blokidde/Blokboy-gaming-device/docs/assets/all_iterations.jpg

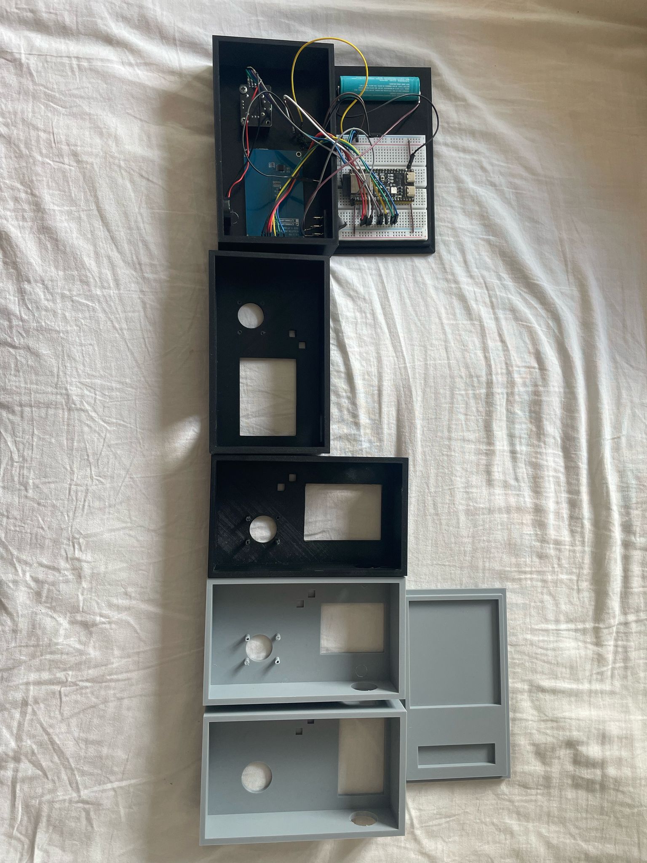
docs/assets/all_iterations.jpg
