blokidde/Blokboy-gaming-device/docs/assets/ardrone.jpeg

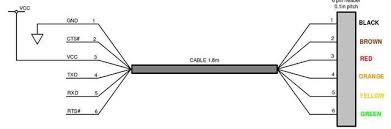
docs/assets/ardrone.jpeg
