blokidde/Blokboy-gaming-device/docs/assets/backpanel_v2.png

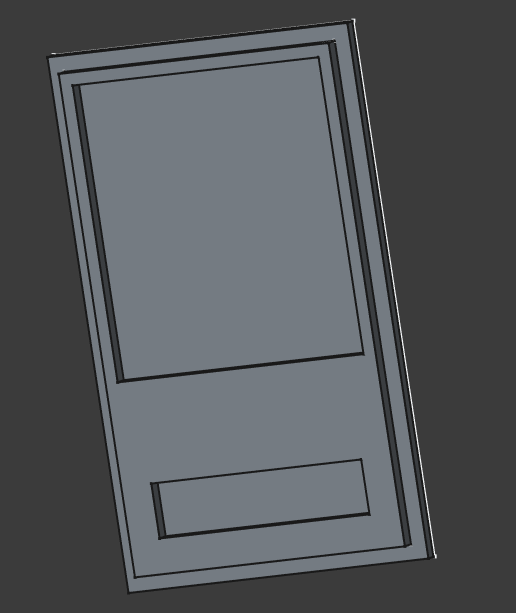
docs/assets/backpanel_v2.png
