blokidde/Blokboy-gaming-device/docs/assets/erd.png

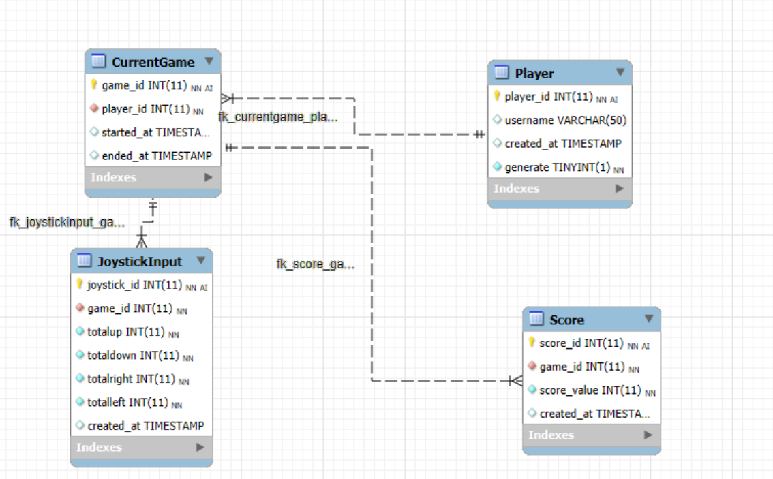
docs/assets/erd.png
