blokidde/Blokboy-gaming-device/docs/assets/frontpanel_v5.png

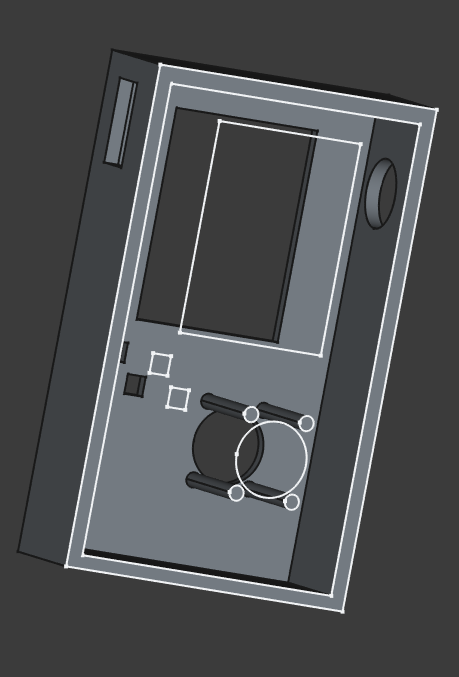
docs/assets/frontpanel_v5.png
