blokidde/Blokboy-gaming-device/docs/assets/http_json_mess.png

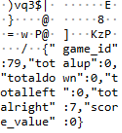
docs/assets/http_json_mess.png
