blokidde/Blokboy-gaming-device/docs/assets/http_message_info.png

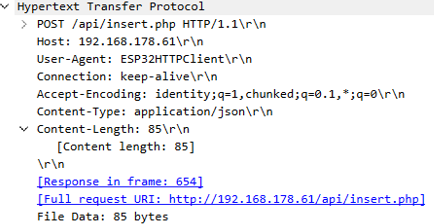
docs/assets/http_message_info.png
