blokidde/Blokboy-gaming-device/docs/assets/http_wireshark.png

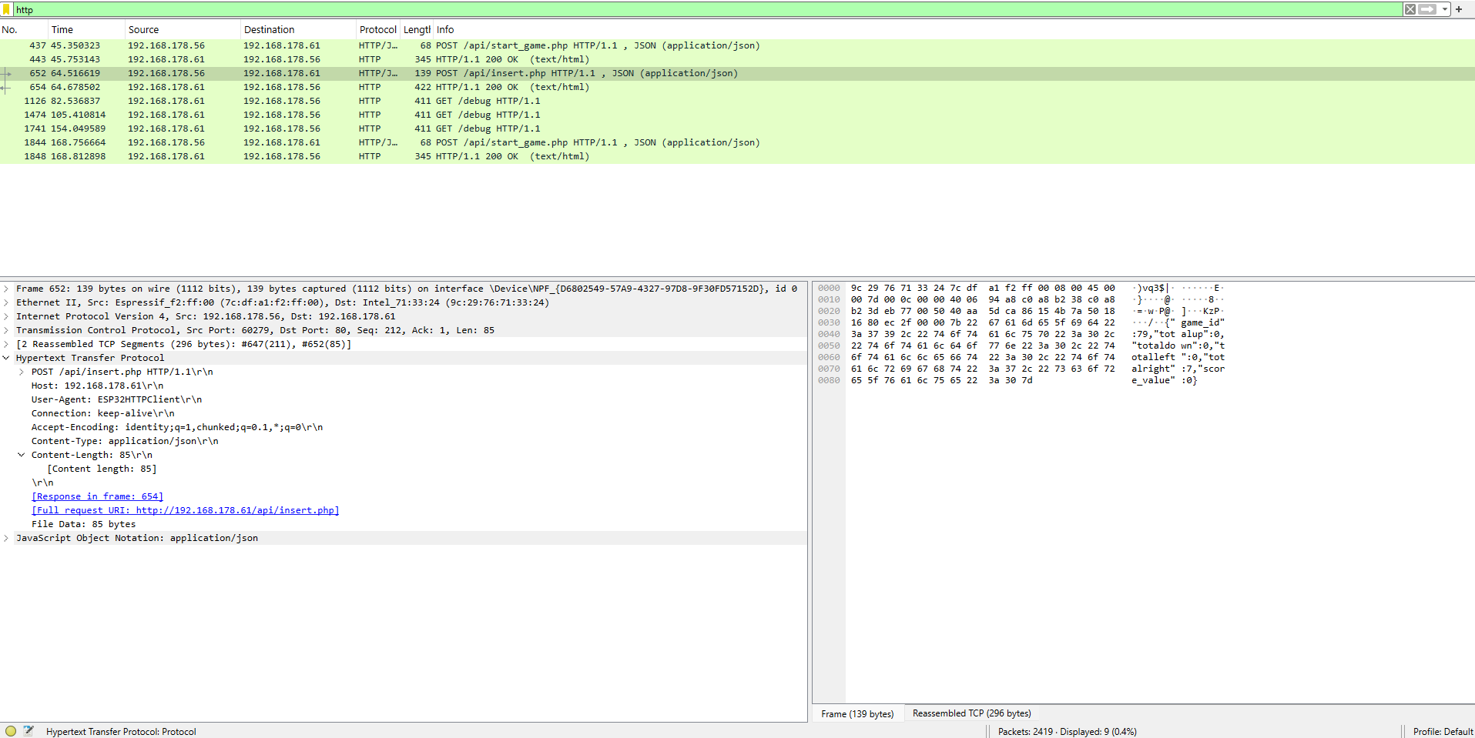
docs/assets/http_wireshark.png
