blokidde/Blokboy-gaming-device/docs/assets/kicad_WD.png

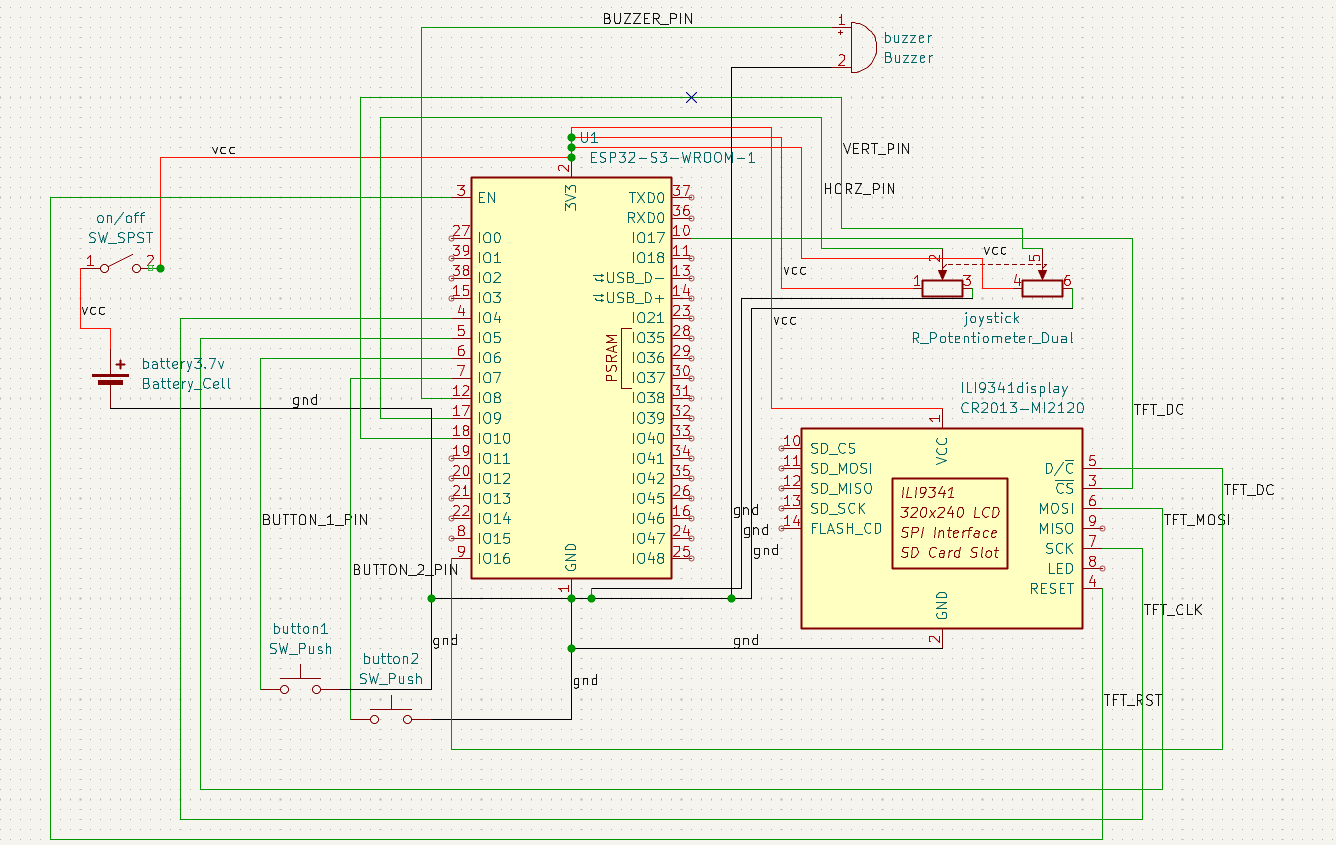
docs/assets/kicad_WD.png
