blokidde/Blokboy-gaming-device/docs/assets/message_HTTPS.png

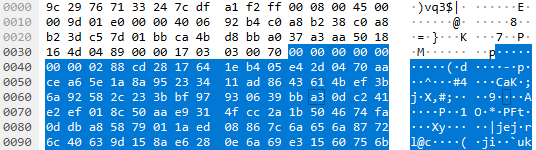
docs/assets/message_HTTPS.png
