blokidde/Blokboy-gaming-device/docs/assets/PlantUml_arch_diagram.png

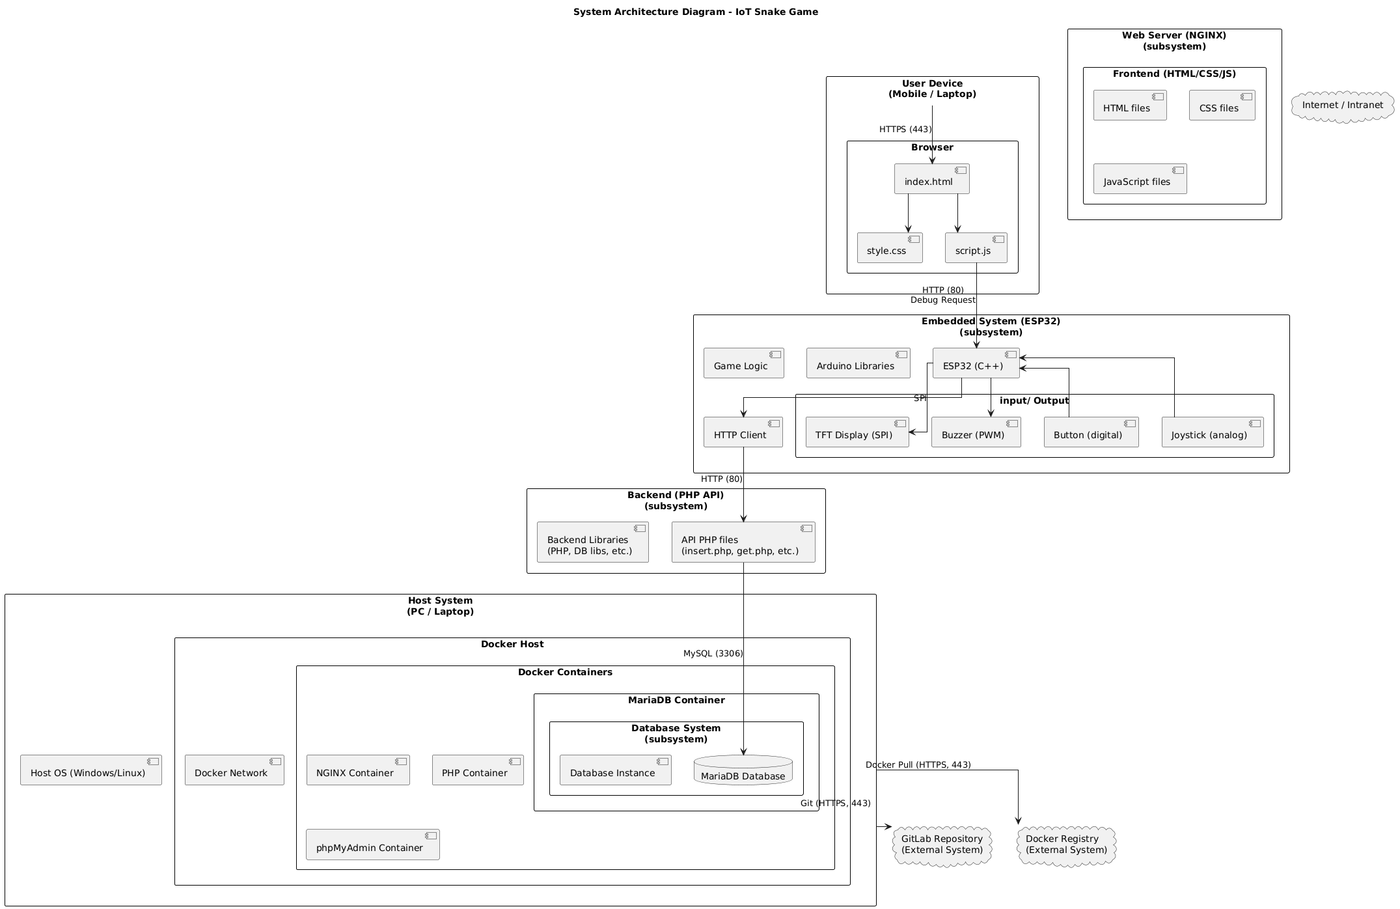
docs/assets/PlantUml_arch_diagram.png
