blokidde/Blokboy-gaming-device/docs/assets/prod_front.jpg

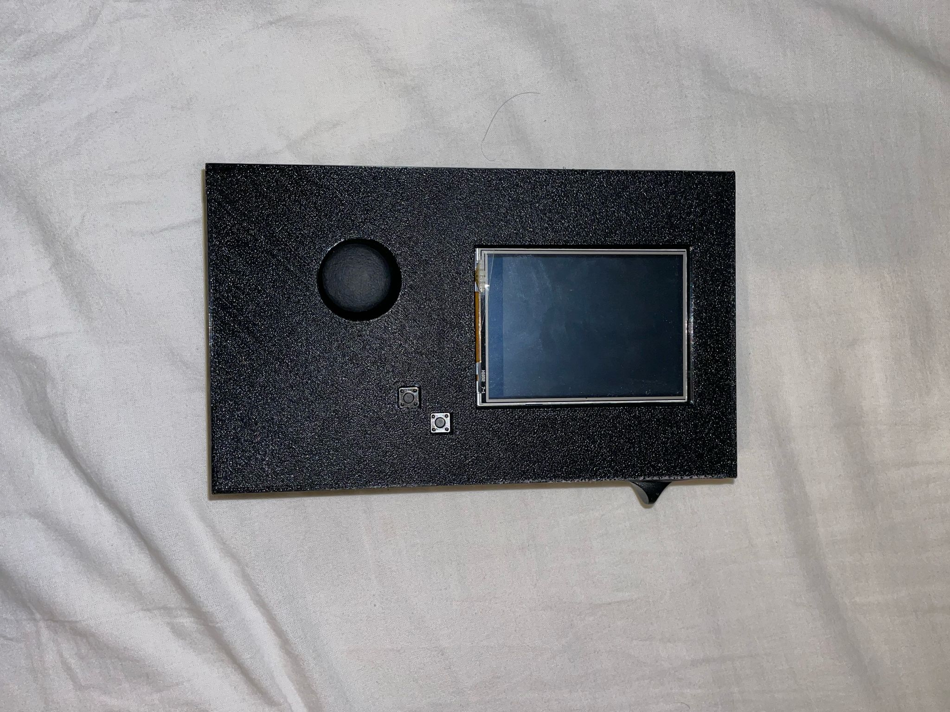
docs/assets/prod_front.jpg
