blokidde/Blokboy-gaming-device/docs/assets/prod_open.jpg

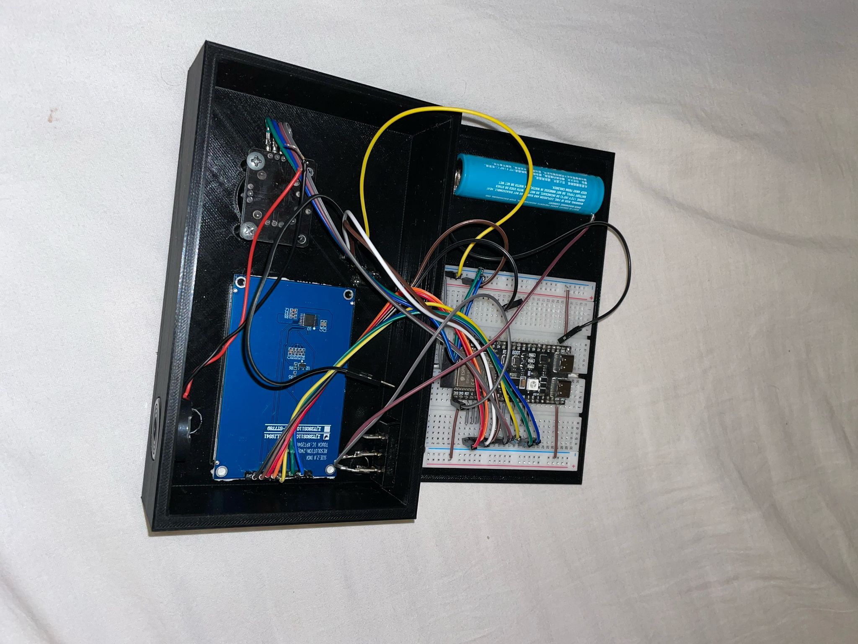
docs/assets/prod_open.jpg
