blokidde/Blokboy-gaming-device/docs/assets/prod_right.jpg

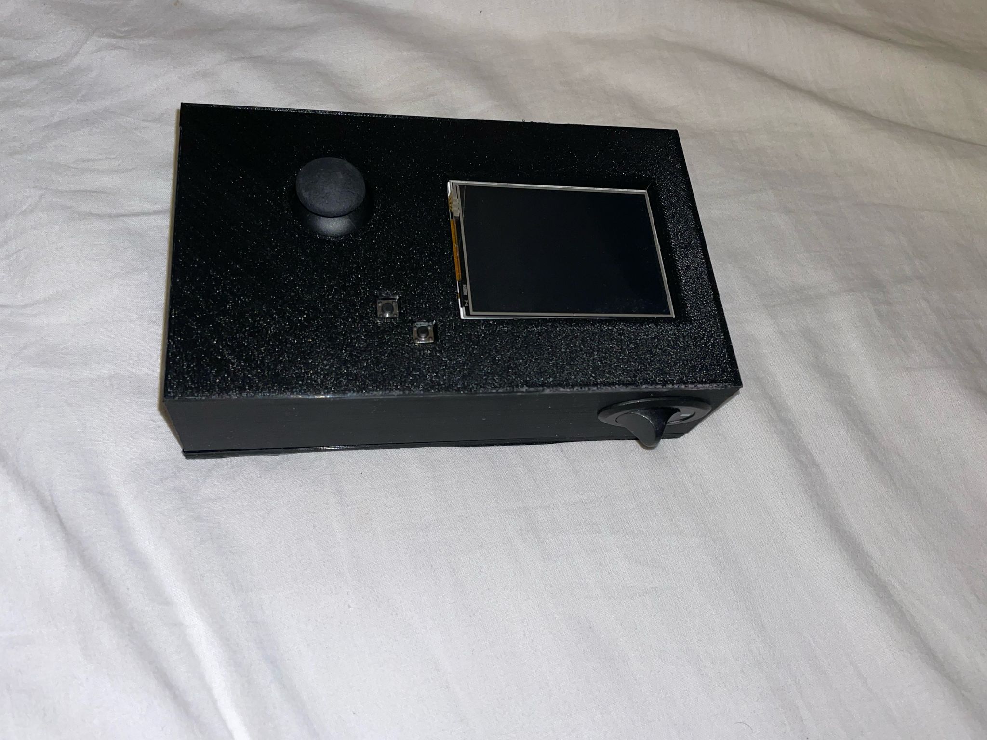
docs/assets/prod_right.jpg
