blokidde/Blokboy-gaming-device/docs/assets/top_HTTPS (3).png

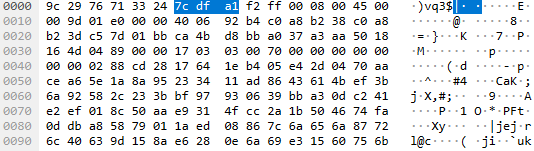
docs/assets/top_HTTPS (3).png
