blokidde/Blokboy-gaming-device/docs/assets/top_HTTPS.png

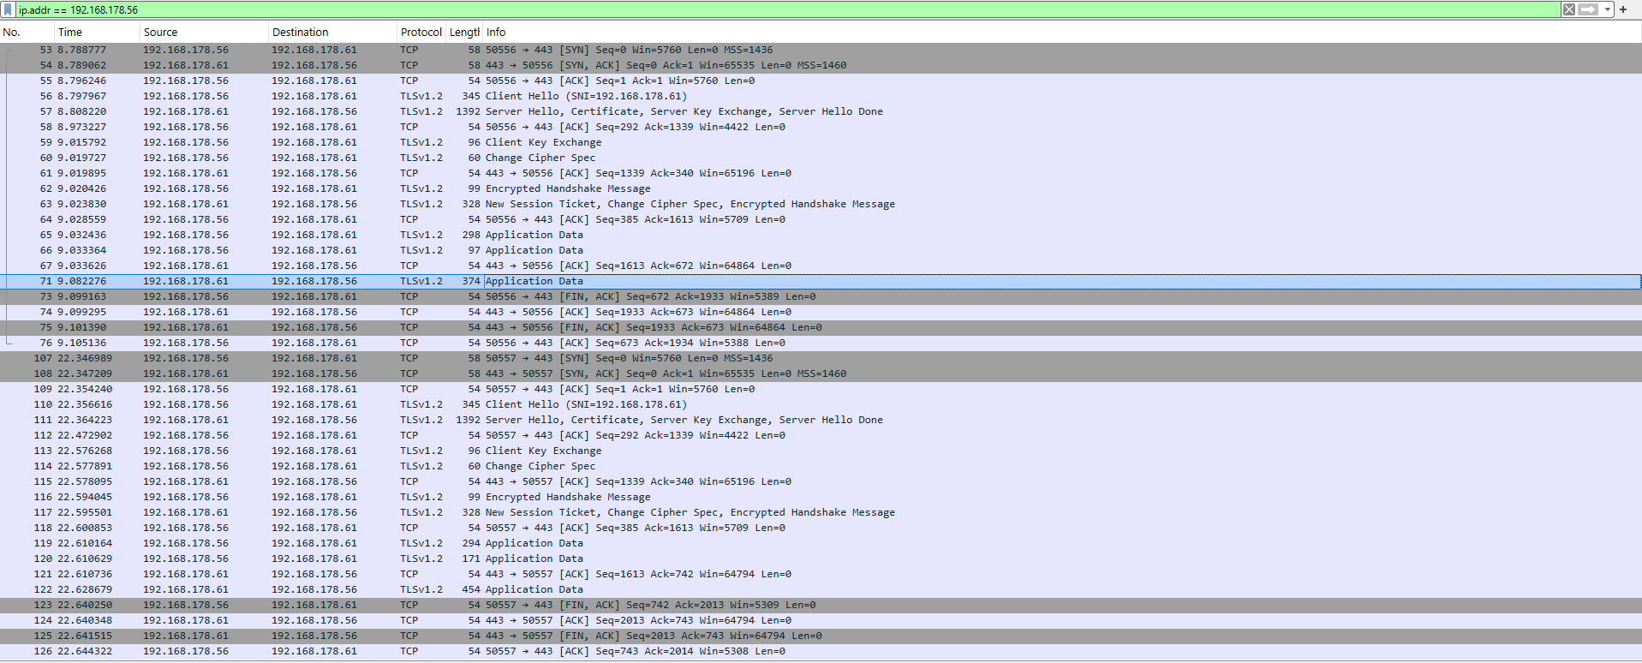
docs/assets/top_HTTPS.png
