blokidde/Blokboy-gaming-device/docs/embedded/fritzing_prototype_blockboy.png

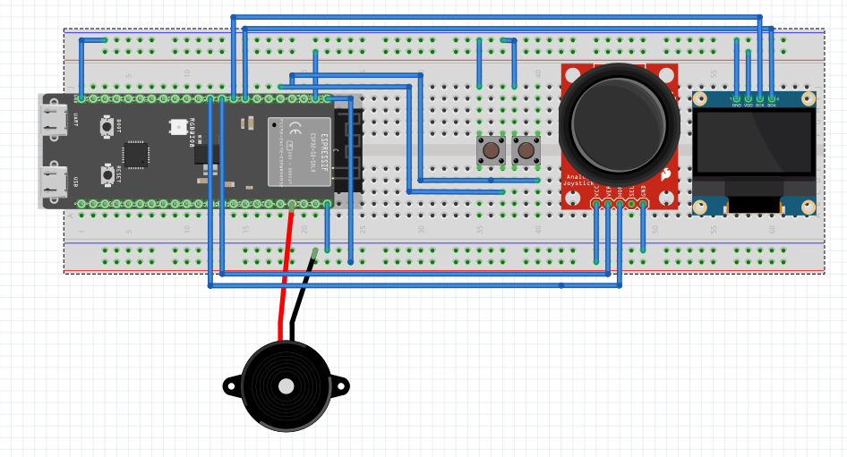
docs/embedded/fritzing_prototype_blockboy.png
